afonsus1997/Inercia-floppy-badge/Software/inercia_badge_sw_tinygl/src/player/player.h

#ifndef __PLAYER__H__
#define __PLAYER__H__

#include "player_config.h"

#include <SPI.h>
#include "AudioGeneratorMOD.h"
#include "AudioOutputI2S.h"
#include "AudioFileSourceSD.h"
#include "io.h"

extern AudioGeneratorMOD *player_mod;
extern AudioFileSourceSD *player_fileO;
extern AudioOutputI2S *player_out;
extern uint16_t player_file_count;
extern char player_now_playing[40];
extern uint16_t player_file_index;


extern File player_root;
extern File player_entry;

void PlayerSetGain(float gain);

void PlayerInit(void);

void PlayerInitSdCard();

void PlayerSetVolume(float volume);

void PlayerHandlePlayback(void);


#endif  //!__PLAYER__H__
