afonsus1997/Inercia-floppy-badge/Software/PlayMODfromSDtoDAC/inercia_bitmap.h

/**
   Inercia logo, inspired by Sinclair Logo
   hand drawn in mtpaint
   
   2024 - Luis Correia (luisfcorreia on github)   
*/

#define INERCIA_W  109
#define INERCIA_H   17

static const uint8_t PROGMEM inercia_bmp[] =
{
  0b00000000, 0b00000000, 0b00000000, 0b00000000, 0b00001110, 0b00000000, 0b00000000, 0b00000000, 0b00000000, 0b00000000, 0b00000000, 0b00000000, 0b00000000, 0b00000000,
  0b00000000, 0b00000000, 0b00000000, 0b00000000, 0b01111110, 0b00000000, 0b00000000, 0b00000000, 0b00000000, 0b00000000, 0b00000000, 0b00000000, 0b00000000, 0b00000000,
  0b01110000, 0b00000000, 0b00000000, 0b00000011, 0b11111110, 0b00000000, 0b00000000, 0b00000000, 0b00000000, 0b00000000, 0b00000111, 0b00000000, 0b00000000, 0b00000000,
  0b01110000, 0b00000000, 0b00000000, 0b00000011, 0b11110000, 0b00000000, 0b00000000, 0b00000000, 0b00000000, 0b00000000, 0b00000111, 0b00000000, 0b00000000, 0b00000000,
  0b01110000, 0b00000000, 0b00000000, 0b00000011, 0b10000000, 0b00000000, 0b00000000, 0b00000000, 0b00000000, 0b00000000, 0b00000111, 0b00000000, 0b00000000, 0b00000000,
  0b00000000, 0b00000000, 0b00000000, 0b00000000, 0b00000000, 0b00000000, 0b00000000, 0b00000000, 0b00000000, 0b00000000, 0b00000000, 0b00000000, 0b00000000, 0b00000000,
  0b01110111, 0b11111111, 0b11111111, 0b01111111, 0b11111111, 0b11110111, 0b11111111, 0b11111111, 0b01111111, 0b11111111, 0b11110111, 0b01111111, 0b11111111, 0b11110000,
  0b01110111, 0b11111111, 0b11111111, 0b01111111, 0b11111111, 0b11110111, 0b11111111, 0b11111111, 0b01111111, 0b11111111, 0b11110111, 0b01111111, 0b11111111, 0b11110000,
  0b01110111, 0b11111111, 0b11111111, 0b01111111, 0b11111111, 0b11110111, 0b11111111, 0b11111111, 0b01111111, 0b11111111, 0b11110111, 0b01111111, 0b11111111, 0b11110000,
  0b01110111, 0b00000000, 0b00000111, 0b01110000, 0b00000000, 0b00000111, 0b00000000, 0b00000000, 0b01110000, 0b00000000, 0b00000111, 0b00000000, 0b00000000, 0b01110000,
  0b01110111, 0b00000000, 0b00000111, 0b01111111, 0b11111111, 0b11110111, 0b00000000, 0b00000000, 0b01110000, 0b00000000, 0b00000111, 0b01111111, 0b11111111, 0b11110000,
  0b01110111, 0b00000000, 0b00000111, 0b01111111, 0b11111111, 0b11110111, 0b00000000, 0b00000000, 0b01110000, 0b00000000, 0b00000111, 0b01111111, 0b11111111, 0b11110000,
  0b01110111, 0b00000000, 0b00000111, 0b01111111, 0b11111111, 0b11110111, 0b00000000, 0b00000000, 0b01110000, 0b00000000, 0b00000111, 0b01111111, 0b11111111, 0b11110000,
  0b01110111, 0b00000000, 0b00000111, 0b01110000, 0b00000000, 0b00000111, 0b00000000, 0b00000000, 0b01110000, 0b00000000, 0b00000111, 0b01110000, 0b00000000, 0b01110000,
  0b01110111, 0b00000000, 0b00000111, 0b01111111, 0b11111111, 0b11110111, 0b00000000, 0b00000000, 0b01111111, 0b11111111, 0b11110111, 0b01111111, 0b11111111, 0b11110000,
  0b01110111, 0b00000000, 0b00000111, 0b01111111, 0b11111111, 0b11110111, 0b00000000, 0b00000000, 0b01111111, 0b11111111, 0b11110111, 0b01111111, 0b11111111, 0b11110000,
  0b01110111, 0b00000000, 0b00000111, 0b01111111, 0b11111111, 0b11110111, 0b00000000, 0b00000000, 0b01111111, 0b11111111, 0b11110111, 0b01111111, 0b11111111, 0b11110000
};
