afonsus1997/Inercia-floppy-badge/Software/inercia_badge_sw_tinygl/src/io/io_config.h

#ifndef __IO_CONFIG__H__
#define __IO_CONFIG__H__

#include <stdint.h>

#define kIoButtonAmmount 3
#define kIoPinAmmountSize 15
#define kIoAnalogInAmmount 1

typedef struct io_pin_config {
  uint8_t pin_number;
  uint8_t pin_mode;
} io_pin_config_t;

typedef struct  {
  uint8_t pin;
  uint8_t state;
  uint8_t lastState;
  unsigned long lastDebounceTime;
  uint8_t activated;
} io_button_t;


typedef enum {
  kIoButtonTop = 0,
  kIoButtonMid = 1,
  kIoButtonBot = 2
} io_button_e;

typedef enum {
  kIoPot = 0,
} io_analog_in_e;


/* externs */
extern const uint8_t kIoPinI2c0Sda;
extern const uint8_t kIoPinI2c0Scl;
extern const uint8_t kIoPinI2c1Sda;
extern const uint8_t kIoPinI2c1Scl;
extern const uint8_t kIoPinOledSda;
extern const uint8_t kIoPinOledScl;
extern const uint8_t kIoPotPin;
extern const uint8_t kIoButtonTopPin;
extern const uint8_t kIoButtonMidPin;
extern const uint8_t kIoButtonBotPin;
extern const uint8_t kIoRngPin;
extern const uint8_t kIoI2sSckPin;
extern const uint8_t kIoRI2sDataPin;
extern io_pin_config_t io_pin_config[kIoPinAmmountSize];
extern io_button_t io_buttons[kIoButtonAmmount];
extern const uint8_t io_analog_pins[kIoAnalogInAmmount];
extern const unsigned long kIoDebounceDelay;
extern const unsigned long KIoVolumeDebounceDelay;
extern const float kIoPotDeadZone;
#endif  //!__IO_CONFIG__H__
