afonsus1997/Inercia-floppy-badge/Software/inercia_badge_sw_tinygl/src/player/player_config.h

#ifndef __PLAYER_CONFIG__H__
#define __PLAYER_CONFIG__H__

#include <stdint.h>

extern const uint16_t kPlayerSampleRate;
extern const uint16_t kPlayerStereoSeparation;
extern const uint16_t kPlayerBufferSize;

#endif  //!__PLAYER_CONFIG__H__
